atp-team/anemone/documentation/images/anemone_prototype_shield_alone_breadboard.png

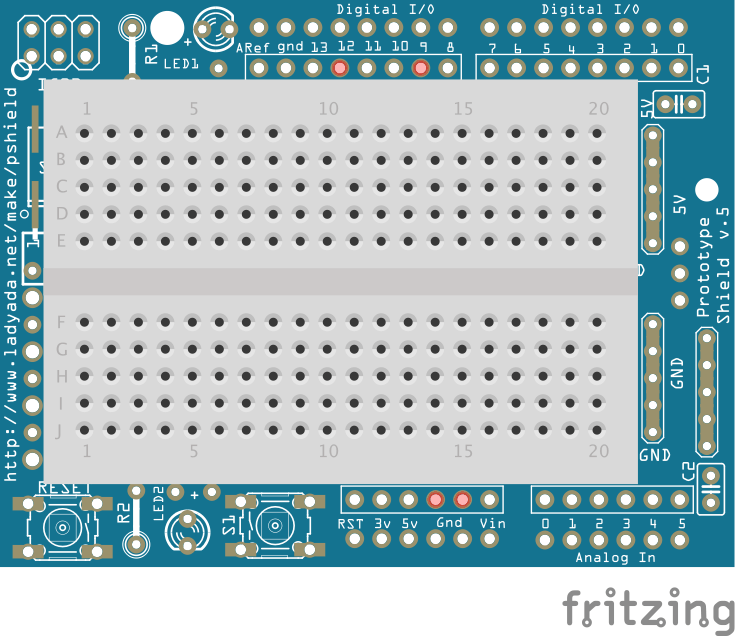
documentation/images/anemone_prototype_shield_alone_breadboard.png
