atp-team/anemone/documentation/images/anemone_prototype_shield_breadboard.png

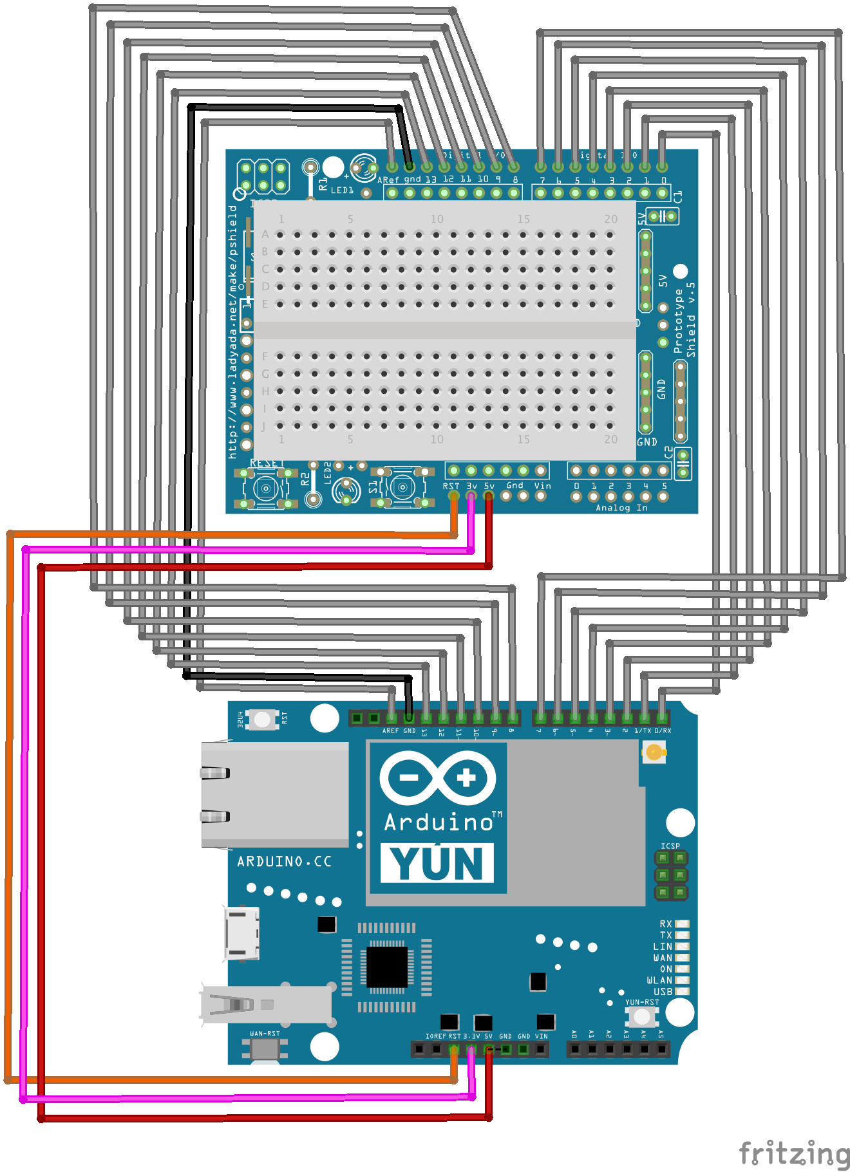
documentation/images/anemone_prototype_shield_breadboard.png
