atp-team/anemone/documentation/images/anemone_prototype_shield_icsp_breadboard.png

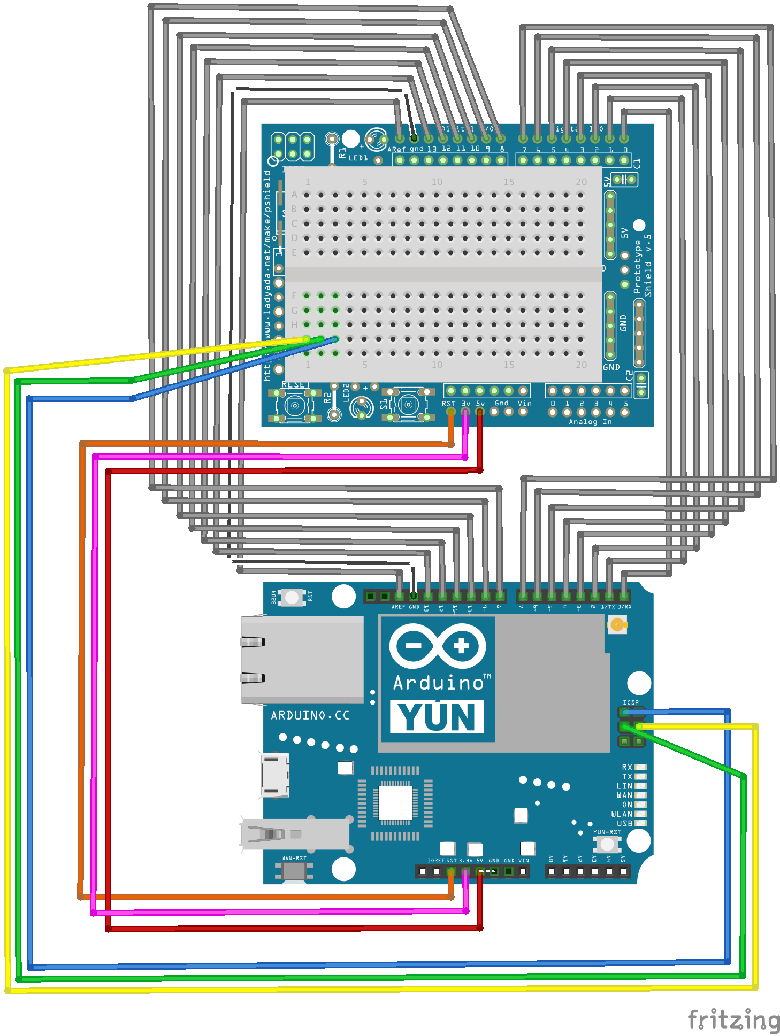
documentation/images/anemone_prototype_shield_icsp_breadboard.png
