atp-team/anemone/documentation/images/Anemone_Tentacle_3D_Visualization.gif

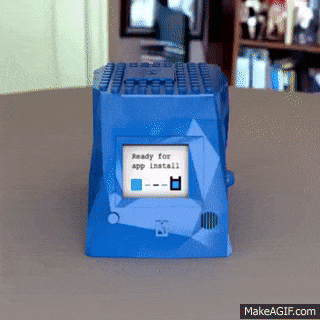
documentation/images/Anemone_Tentacle_3D_Visualization.gif
