atp-team/anemone/documentation/images/anemone_tentacle_display_board_breadboard.png

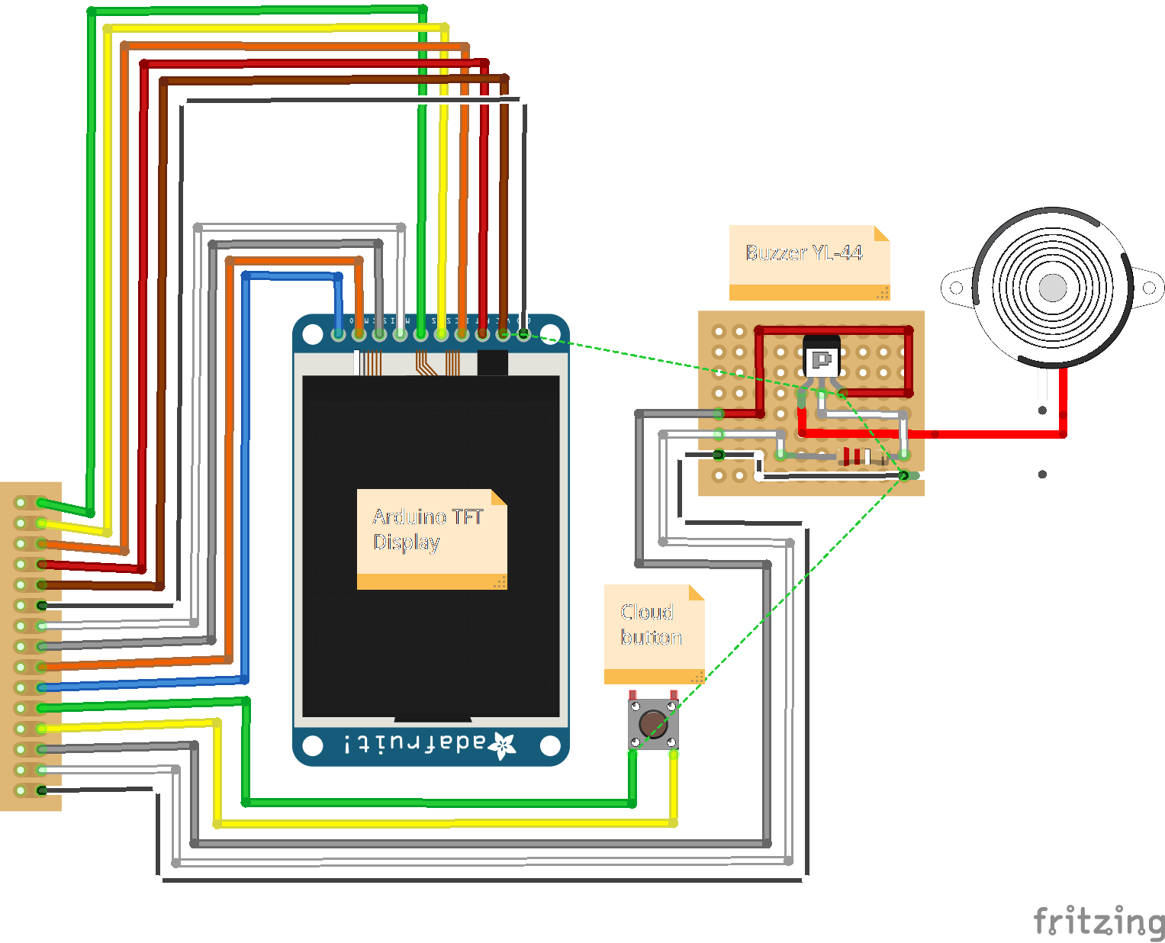
documentation/images/anemone_tentacle_display_board_breadboard.png
