atp-team/anemone/documentation/images/anemone_tentacle_rj11_i2C_breadboard.png

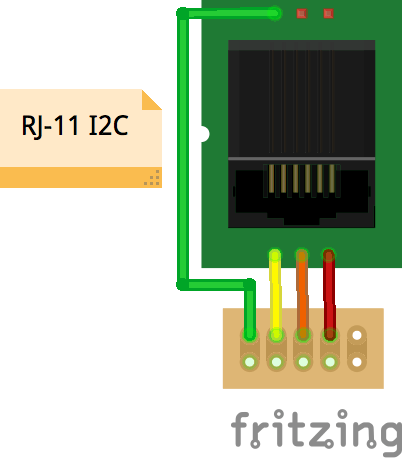
documentation/images/anemone_tentacle_rj11_i2C_breadboard.png
