atp-team/anemone/documentation/images/anemone_tentacle_shield_alone_breadboard.png

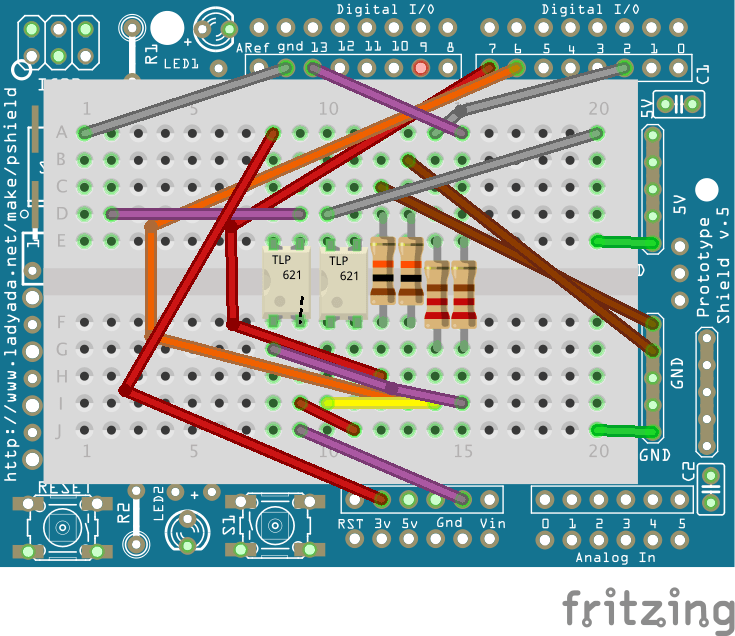
documentation/images/anemone_tentacle_shield_alone_breadboard.png
