atp-team/anemone/documentation/images/renders/numbered/left.png

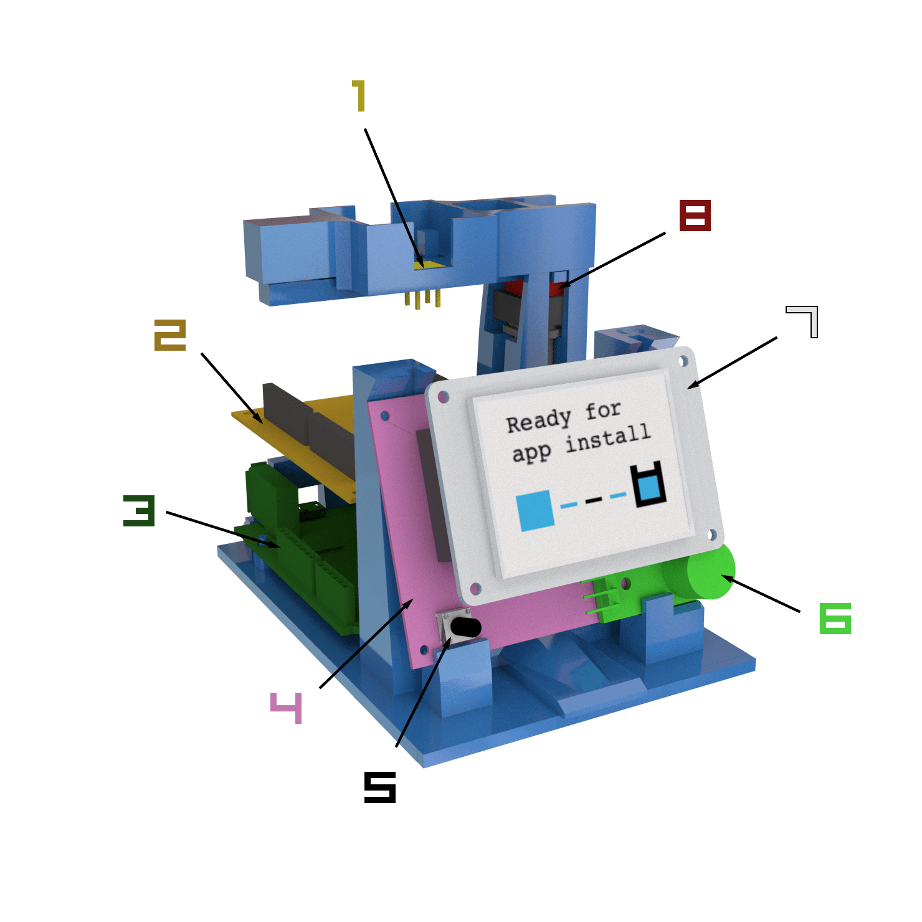
documentation/images/renders/numbered/left.png
