atp-team/anemone/documentation/images/renders/numbered/right.png

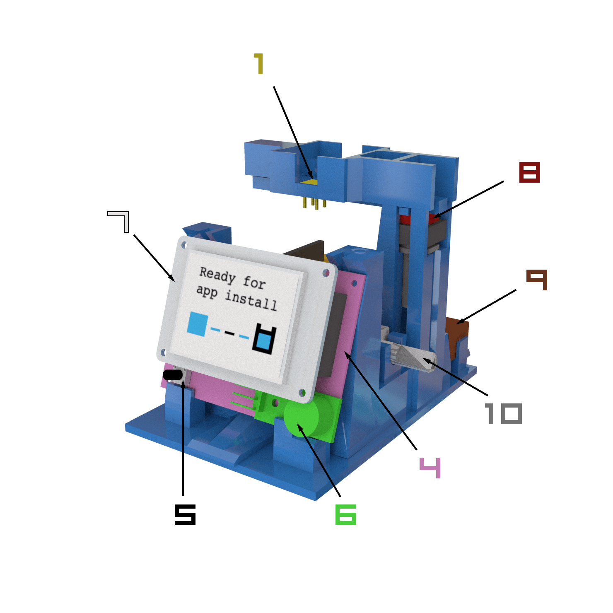
documentation/images/renders/numbered/right.png
