atp-team/anemone/documentation/images/tentacle_matte.png

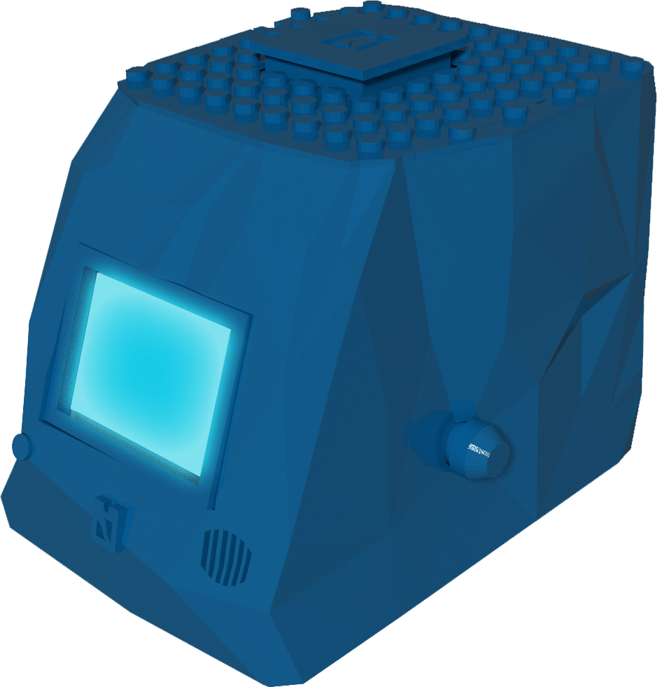
documentation/images/tentacle_matte.png
