atp-team/anemone/documentation/images/tentacle_shield_wires.JPG

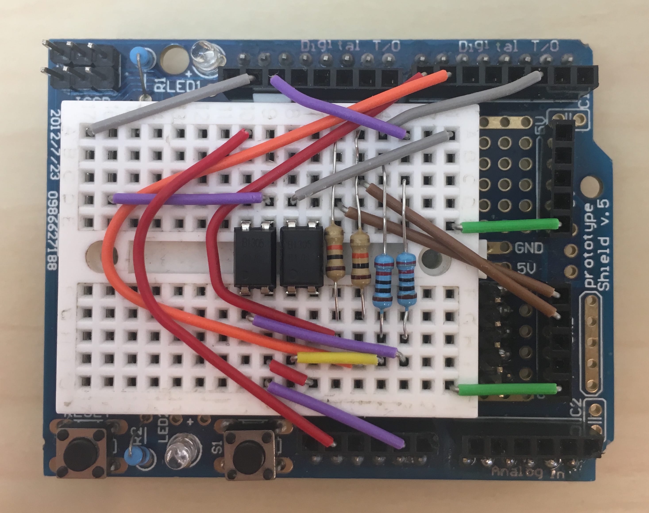
documentation/images/tentacle_shield_wires.JPG
