atp-team/anemone/documentation/images/anemone_tentacle_shield_wiring_no_icsp_breadboard.png

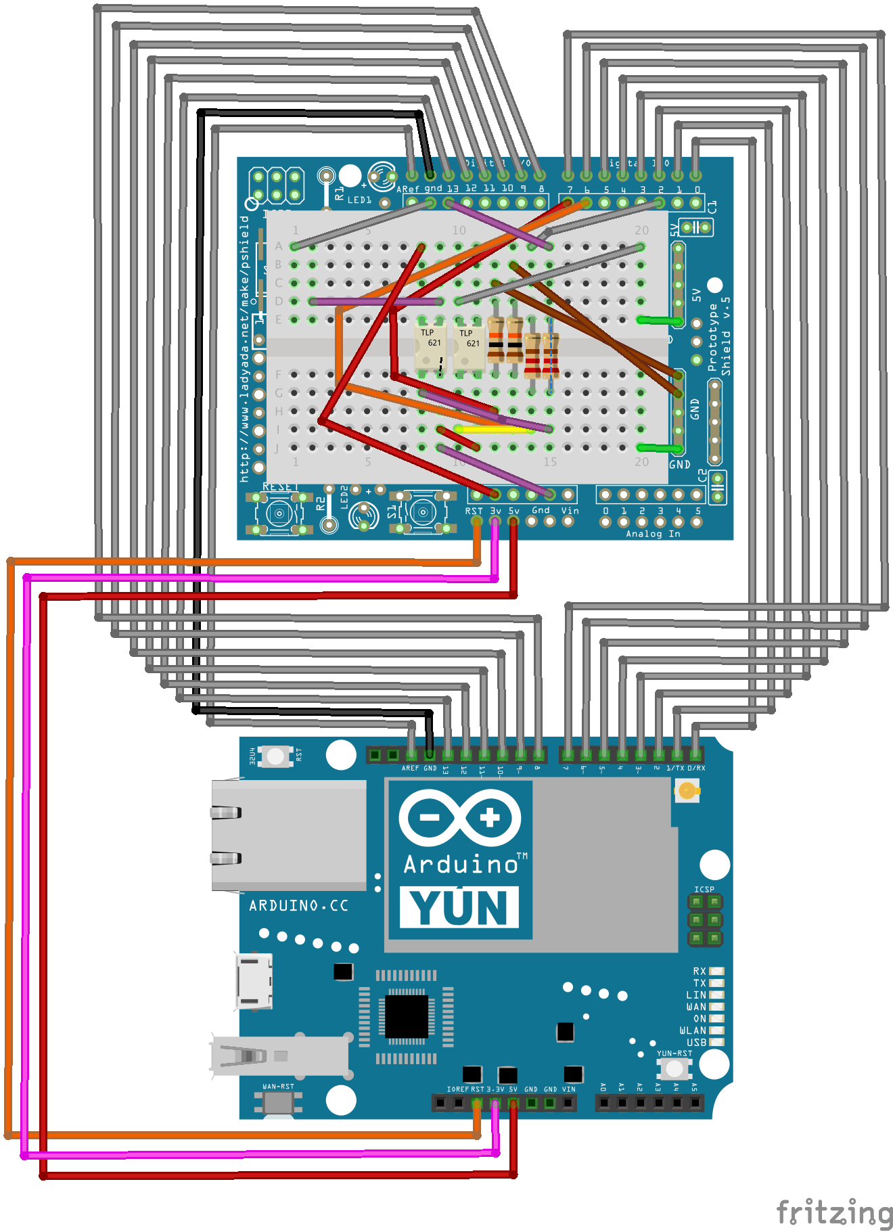
documentation/images/anemone_tentacle_shield_wiring_no_icsp_breadboard.png
