atp-team/anemone/documentation/images/printed/3_printed_top.jpg

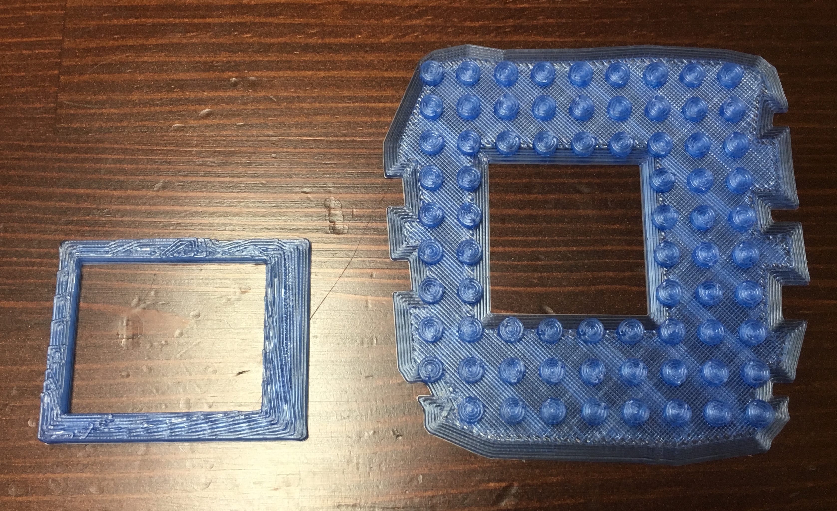
documentation/images/printed/3_printed_top.jpg
